PandaKBLab/Lily58-Glow-Enc-Wireless/pcb/Lily58.kicad_sch

## KiCad design pcb/Lily58.kicad_sch (2022-09-28)

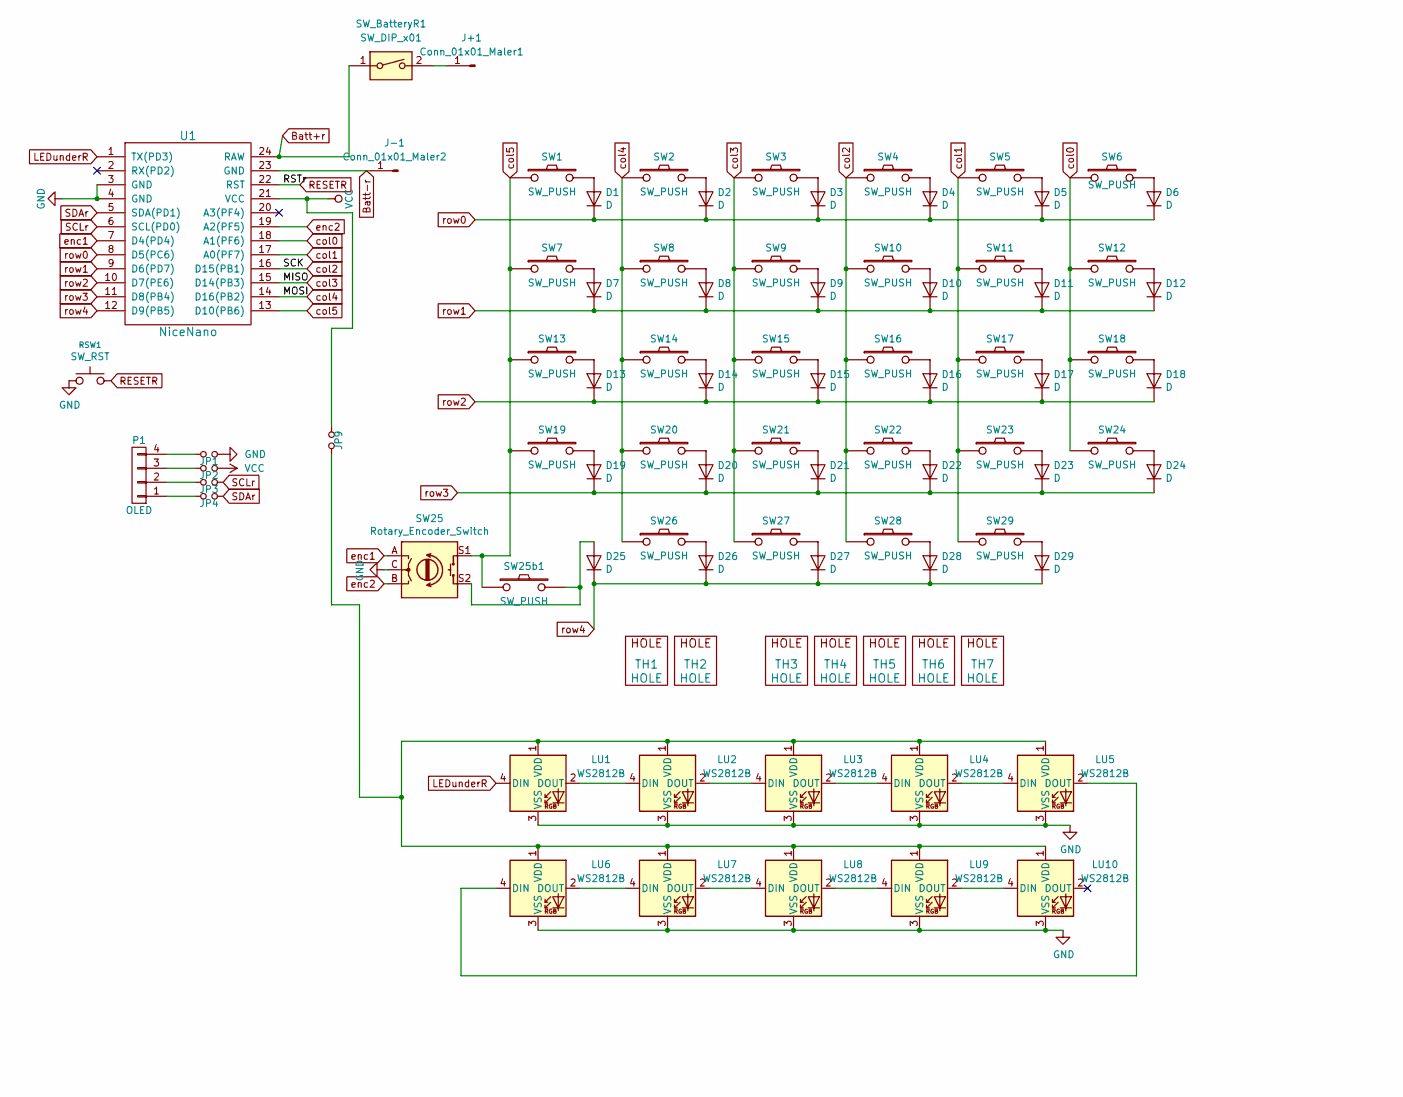
[picture p2: schematic Lily58.kicad_sch, part in row 1, column 1]

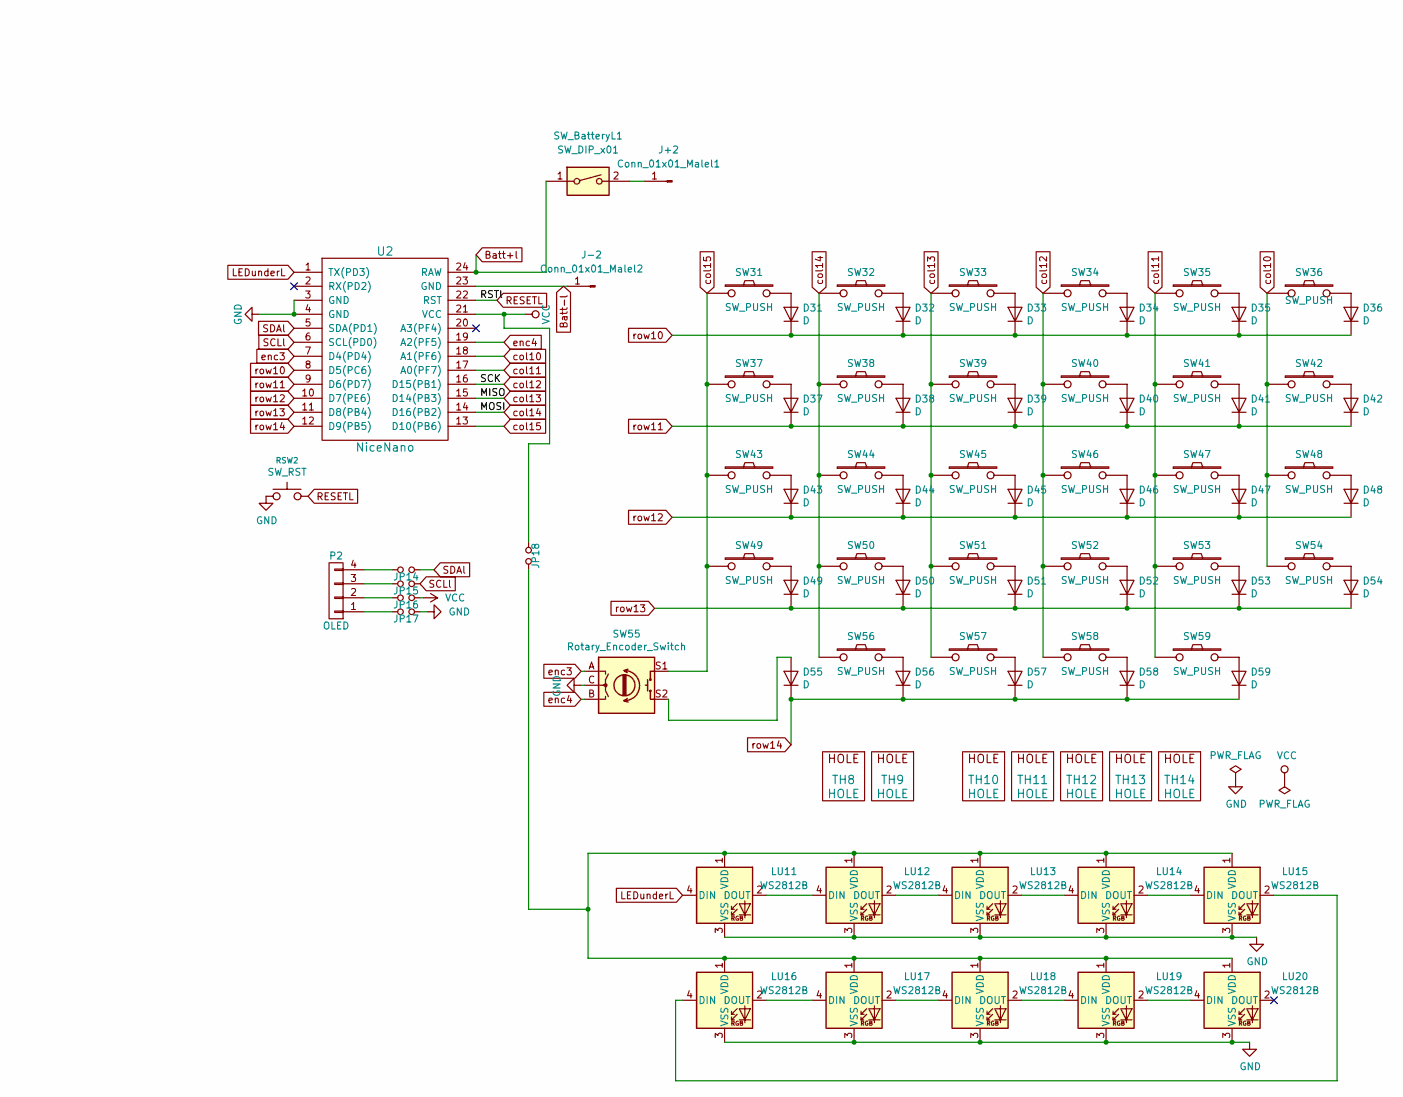
[picture p3: schematic Lily58.kicad_sch, part in row 1, column 2]

Parts:
D1, D2, D3, D4, D5, D6, D7, D8, D9, D10, D11, D12, D13, D14, D15, D16, D17, D18, D19, D20, D21, D22, D23, D24, D25, D26, D27, D28, D29, D31, D32, D33, D34, D35, D36, D37, D38, D39, D40, D41, D42, D43, D44, D45, D46, D47, D48, D49, D50, D51, D52, D53, D54, D55, D56, D57, D58, D59: D; D_SOD-123-Pretty
J+1: Conn_01x01_Maler1; TestPoint_Pad_2.0x2.0mm
J+2: Conn_01x01_Malel1; TestPoint_Pad_2.0x2.0mm
J-1: Conn_01x01_Maler2; TestPoint_Pad_2.0x2.0mm
J-2: Conn_01x01_Malel2; TestPoint_Pad_2.0x2.0mm
JP1, JP2, JP3, JP4, JP9, JP14, JP15, JP16, JP17, JP18: Jumper_NO_Small; Jumper
LU1, LU2, LU3, LU4, LU5, LU6, LU7, LU8, LU9, LU10, LU11, LU12, LU13, LU14, LU15, LU16, LU17, LU18, LU19, LU20: WS2812B; LED_WS2812B_PLCC4_5.0x5.0mm_P3.2mm
P1, P2: OLED; MY_SIL-4
RSW1, RSW2: SW_RST; TACT_SWITCH_TVBP06
SW1, SW2, SW3, SW4, SW5, SW6, SW7, SW8, SW9, SW10, SW11, SW12, SW13, SW14, SW15, SW16, SW17, SW18, SW19, SW20, SW21, SW22, SW23, SW24, SW26, SW27, SW28, SW29, SW31, SW32, SW33, SW34, SW35, SW36, SW37, SW38, SW39, SW40, SW41, SW42, SW43, SW44, SW45, SW46, SW47, SW48, SW49, SW50, SW51, SW52, SW53, SW54, SW56, SW57, SW58, SW59: SW_PUSH; MX_Socket_18mm
SW25, SW55: Rotary_Encoder_Switch; RotaryEncoder_Alps_EC11E-Switch_Vertical_H20mm
SW25b1: SW_PUSH; SW_Cherry_MX_1.00u_PCB
SW_BatteryL1: SW_DIP_x01; SW_CuK_OS102011MA1QN1_SPDT_Angled
SW_BatteryR1: SW_DIP_x01; SW_CuK_OS102011MA1QN1_SPDT_Angled
TH1, TH2, TH8, TH9: HOLE; HOLE_M2
TH3, TH4, TH5, TH6, TH7, TH10, TH11, TH12, TH13, TH14: HOLE; HOLE_M2_TH
U1, U2: NiceNano; nice_nano

Connections:
Batt+l: SW_BatteryL1.1, U2.24 (RAW)
Batt+r: SW_BatteryR1.1, U1.24 (RAW)
Batt-l: J-2.1, U2.23 (GND)
Batt-r: J-1.1, U1.23 (GND)
GND: JP1.2, JP17.2, LU1.3 (VSS), LU2.3 (VSS), LU3.3 (VSS), LU4.3 (VSS), LU5.3 (VSS), LU6.3 (VSS), LU7.3 (VSS), LU8.3 (VSS), LU9.3 (VSS), LU10.3 (VSS), LU11.3 (VSS), LU12.3 (VSS), LU13.3 (VSS), LU14.3 (VSS), LU15.3 (VSS), LU16.3 (VSS), LU17.3 (VSS), LU18.3 (VSS), LU19.3 (VSS), LU20.3 (VSS), RSW1.1, RSW2.1, SW25.C, SW55.C, U1.3 (GND), U1.4 (GND), U2.3 (GND), U2.4 (GND)
LEDunderL: LU11.4 (DIN), U2.1 (TX(PD3))
LEDunderR: LU1.4 (DIN), U1.1 (TX(PD3))
unnamed: D1.2 (A), SW1.2
unnamed: D2.2 (A), SW2.2
unnamed: D3.2 (A), SW3.2
unnamed: D4.2 (A), SW4.2
unnamed: D5.2 (A), SW5.2
unnamed: D6.2 (A), SW6.2
unnamed: D7.2 (A), SW7.2
unnamed: D8.2 (A), SW8.2
unnamed: D9.2 (A), SW9.2
unnamed: D10.2 (A), SW10.2
unnamed: D11.2 (A), SW11.2
unnamed: D12.2 (A), SW12.2
unnamed: D13.2 (A), SW13.2
unnamed: D14.2 (A), SW14.2
unnamed: D15.2 (A), SW15.2
unnamed: D16.2 (A), SW16.2
unnamed: D17.2 (A), SW17.2
unnamed: D18.2 (A), SW18.2
unnamed: D19.2 (A), SW19.2
unnamed: D20.2 (A), SW20.2
unnamed: D21.2 (A), SW21.2
unnamed: D22.2 (A), SW22.2
unnamed: D23.2 (A), SW23.2
unnamed: D24.2 (A), SW24.2
unnamed: D25.2 (A), SW25.S2, SW25b1.2
unnamed: D26.2 (A), SW26.2
unnamed: D27.2 (A), SW27.2
unnamed: D28.2 (A), SW28.2
unnamed: D29.2 (A), SW29.2
unnamed: D31.2 (A), SW31.2
unnamed: D32.2 (A), SW32.2
unnamed: D33.2 (A), SW33.2
unnamed: D34.2 (A), SW34.2
unnamed: D35.2 (A), SW35.2
unnamed: D36.2 (A), SW36.2
unnamed: D37.2 (A), SW37.2
unnamed: D38.2 (A), SW38.2
unnamed: D39.2 (A), SW39.2
unnamed: D40.2 (A), SW40.2
unnamed: D41.2 (A), SW41.2
unnamed: D42.2 (A), SW42.2
unnamed: D43.2 (A), SW43.2
unnamed: D44.2 (A), SW44.2
unnamed: D45.2 (A), SW45.2
unnamed: D46.2 (A), SW46.2
unnamed: D47.2 (A), SW47.2
unnamed: D48.2 (A), SW48.2
unnamed: D49.2 (A), SW49.2
unnamed: D50.2 (A), SW50.2
unnamed: D51.2 (A), SW51.2
unnamed: D52.2 (A), SW52.2
unnamed: D53.2 (A), SW53.2
unnamed: D54.2 (A), SW54.2
unnamed: D55.2 (A), SW55.S2
unnamed: D56.2 (A), SW56.2
unnamed: D57.2 (A), SW57.2
unnamed: D58.2 (A), SW58.2
unnamed: D59.2 (A), SW59.2
unnamed: J+1.1, SW_BatteryR1.2
unnamed: J+2.1, SW_BatteryL1.2
unnamed: JP1.1, P1.4
unnamed: JP2.1, P1.3
unnamed: JP3.1, P1.2
unnamed: JP4.1, P1.1
unnamed: JP9.1, LU1.1 (VDD), LU2.1 (VDD), LU3.1 (VDD), LU4.1 (VDD), LU5.1 (VDD), LU6.1 (VDD), LU7.1 (VDD), LU8.1 (VDD), LU9.1 (VDD), LU10.1 (VDD)
unnamed: JP14.1, P2.4
unnamed: JP15.1, P2.3
unnamed: JP16.1, P2.2
unnamed: JP17.1, P2.1
unnamed: JP18.1, LU11.1 (VDD), LU12.1 (VDD), LU13.1 (VDD), LU14.1 (VDD), LU15.1 (VDD), LU16.1 (VDD), LU17.1 (VDD), LU18.1 (VDD), LU19.1 (VDD), LU20.1 (VDD)
unnamed: LU1.2 (DOUT), LU2.4 (DIN)
unnamed: LU2.2 (DOUT), LU3.4 (DIN)
unnamed: LU3.2 (DOUT), LU4.4 (DIN)
unnamed: LU4.2 (DOUT), LU5.4 (DIN)
unnamed: LU5.2 (DOUT), LU6.4 (DIN)
unnamed: LU6.2 (DOUT), LU7.4 (DIN)
unnamed: LU7.2 (DOUT), LU8.4 (DIN)
unnamed: LU8.2 (DOUT), LU9.4 (DIN)
unnamed: LU9.2 (DOUT), LU10.4 (DIN)
unnamed: LU11.2 (DOUT), LU12.4 (DIN)
unnamed: LU12.2 (DOUT), LU13.4 (DIN)
unnamed: LU13.2 (DOUT), LU14.4 (DIN)
unnamed: LU14.2 (DOUT), LU15.4 (DIN)
unnamed: LU15.2 (DOUT), LU16.4 (DIN)
unnamed: LU16.2 (DOUT), LU17.4 (DIN)
unnamed: LU17.2 (DOUT), LU18.4 (DIN)
unnamed: LU18.2 (DOUT), LU19.4 (DIN)
unnamed: LU19.2 (DOUT), LU20.4 (DIN)
RESETL: RSW2.2, U2.22 (RST)
RESETR: RSW1.2, U1.22 (RST)
SCLl: JP15.2, U2.6 (SCL(PD0))
SCLr: JP3.2, U1.6 (SCL(PD0))
SDAl: JP14.2, U2.5 (SDA(PD1))
SDAr: JP4.2, U1.5 (SDA(PD1))
VCC: JP2.2, JP9.2, JP16.2, JP18.2, U1.21 (VCC), U2.21 (VCC)
col0: SW6.1, SW12.1, SW18.1, SW24.1, U1.18 (A1(PF6))
col1: SW5.1, SW11.1, SW17.1, SW23.1, SW29.1, U1.17 (A0(PF7))
col5: SW1.1, SW7.1, SW13.1, SW19.1, SW25.S1, SW25b1.1, U1.13 (D10(PB6))
col10: SW36.1, SW42.1, SW48.1, SW54.1, U2.18 (A1(PF6))
col11: SW35.1, SW41.1, SW47.1, SW53.1, SW59.1, U2.17 (A0(PF7))
col12: SW4.1, SW10.1, SW16.1, SW22.1, SW28.1, SW34.1, SW40.1, SW46.1, SW52.1, SW58.1, U1.16 (D15(PB1)), U2.16 (D15(PB1))
col13: SW3.1, SW9.1, SW15.1, SW21.1, SW27.1, SW33.1, SW39.1, SW45.1, SW51.1, SW57.1, U1.15 (D14(PB3)), U2.15 (D14(PB3))
col14: SW2.1, SW8.1, SW14.1, SW20.1, SW26.1, SW32.1, SW38.1, SW44.1, SW50.1, SW56.1, U1.14 (D16(PB2)), U2.14 (D16(PB2))
col15: SW31.1, SW37.1, SW43.1, SW49.1, SW55.S1, U2.13 (D10(PB6))
enc1: SW25.A, U1.7 (D4(PD4))
enc2: SW25.B, U1.19 (A2(PF5))
enc3: SW55.A, U2.7 (D4(PD4))
enc4: SW55.B, U2.19 (A2(PF5))
row0: D1.1 (K), D2.1 (K), D3.1 (K), D4.1 (K), D5.1 (K), D6.1 (K), U1.8 (D5(PC6))
row1: D7.1 (K), D8.1 (K), D9.1 (K), D10.1 (K), D11.1 (K), D12.1 (K), U1.9 (D6(PD7))
row2: D13.1 (K), D14.1 (K), D15.1 (K), D16.1 (K), D17.1 (K), D18.1 (K), U1.10 (D7(PE6))
row3: D19.1 (K), D20.1 (K), D21.1 (K), D22.1 (K), D23.1 (K), D24.1 (K), U1.11 (D8(PB4))
row4: D25.1 (K), D26.1 (K), D27.1 (K), D28.1 (K), D29.1 (K), U1.12 (D9(PB5))
row10: D31.1 (K), D32.1 (K), D33.1 (K), D34.1 (K), D35.1 (K), D36.1 (K), U2.8 (D5(PC6))
row11: D37.1 (K), D38.1 (K), D39.1 (K), D40.1 (K), D41.1 (K), D42.1 (K), U2.9 (D6(PD7))
row12: D43.1 (K), D44.1 (K), D45.1 (K), D46.1 (K), D47.1 (K), D48.1 (K), U2.10 (D7(PE6))
row13: D49.1 (K), D50.1 (K), D51.1 (K), D52.1 (K), D53.1 (K), D54.1 (K), U2.11 (D8(PB4))
row14: D55.1 (K), D56.1 (K), D57.1 (K), D58.1 (K), D59.1 (K), U2.12 (D9(PB5))
